ampnics/CAN-to-WiFi-Converter-Dongle-/ESP32_Wifi2CAN_Rev0.1/Docs/Bottom_Layout.png

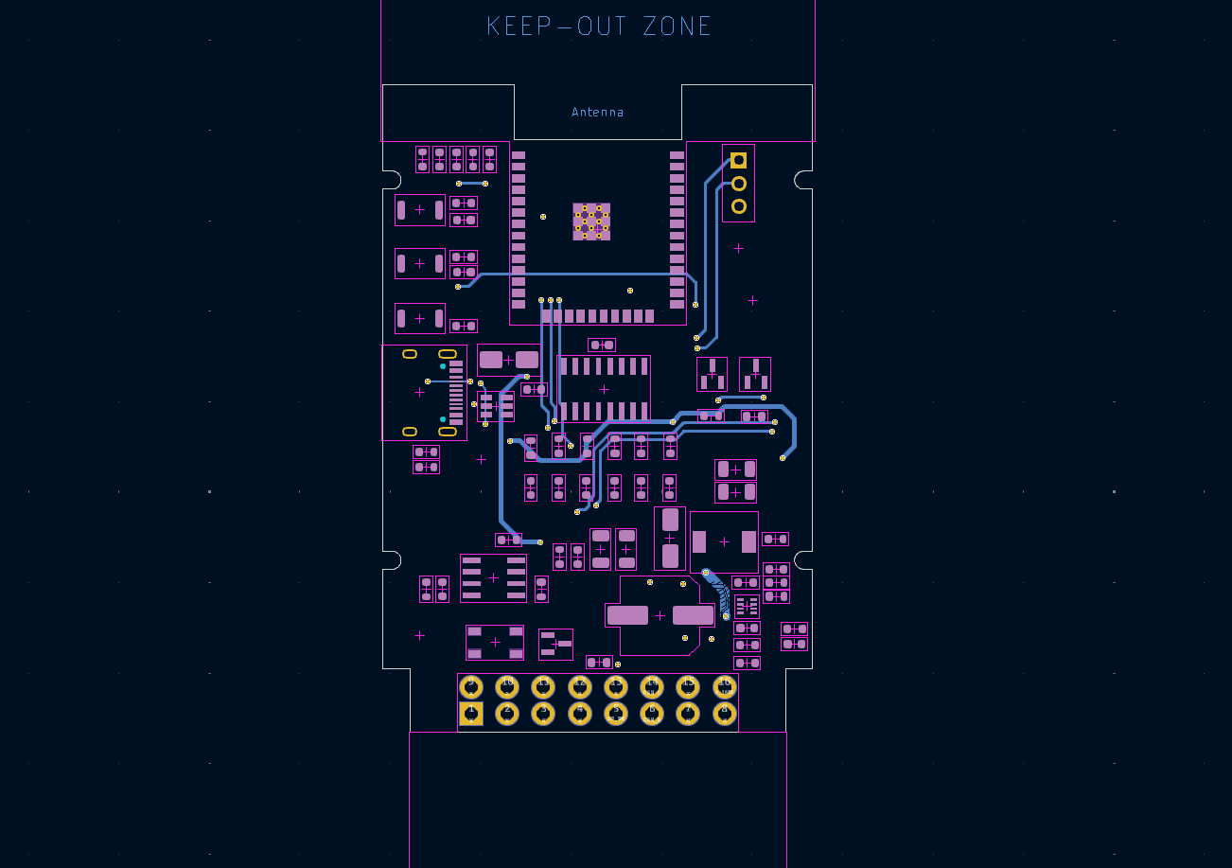
ESP32_Wifi2CAN_Rev0.1/Docs/Bottom_Layout.png
